giacomos97/Nadetech-to-Cheersonic-USC/resources/RS485_connections.png

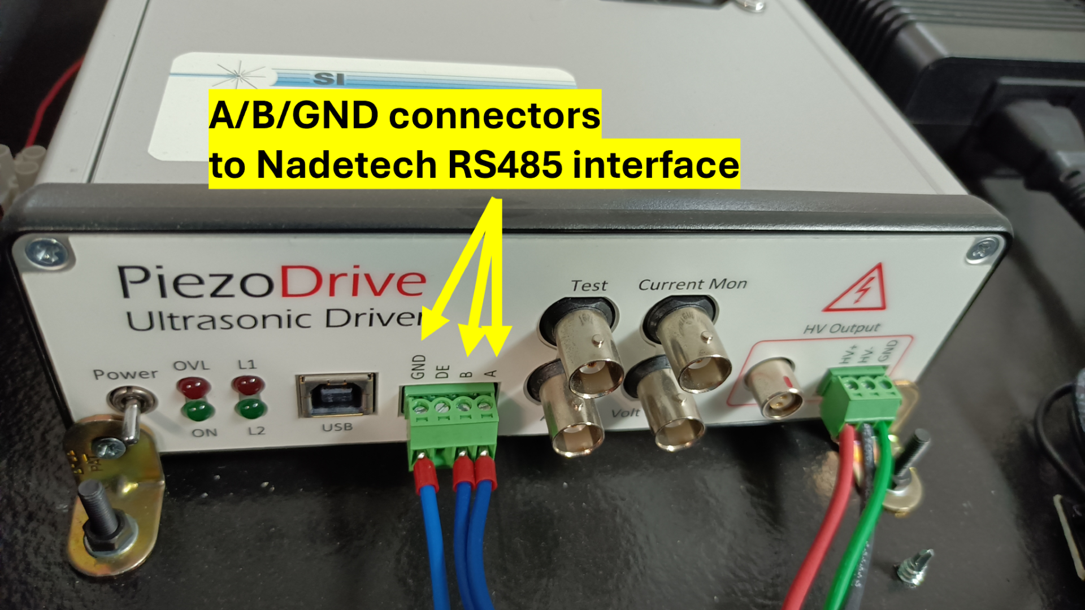
resources/RS485_connections.png
