giacomos97/Nadetech-to-Cheersonic-USC/resources/US_generator_configuration.png

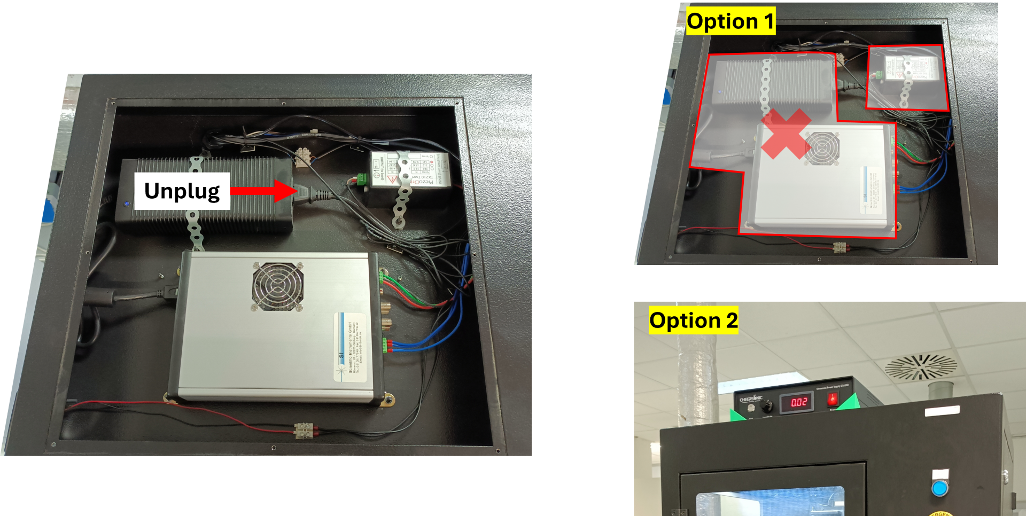
resources/US_generator_configuration.png
