giacomos97/Nadetech-to-Cheersonic-USC/resources/USB_cable_connections.png

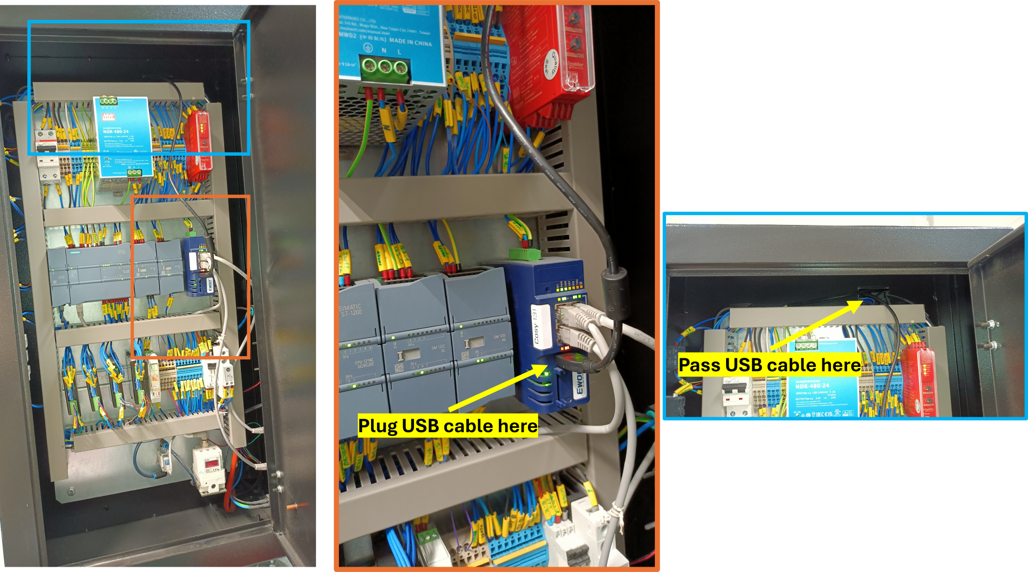
resources/USB_cable_connections.png
